BrianEnigma/chubby-tricorder/Images/probe.png

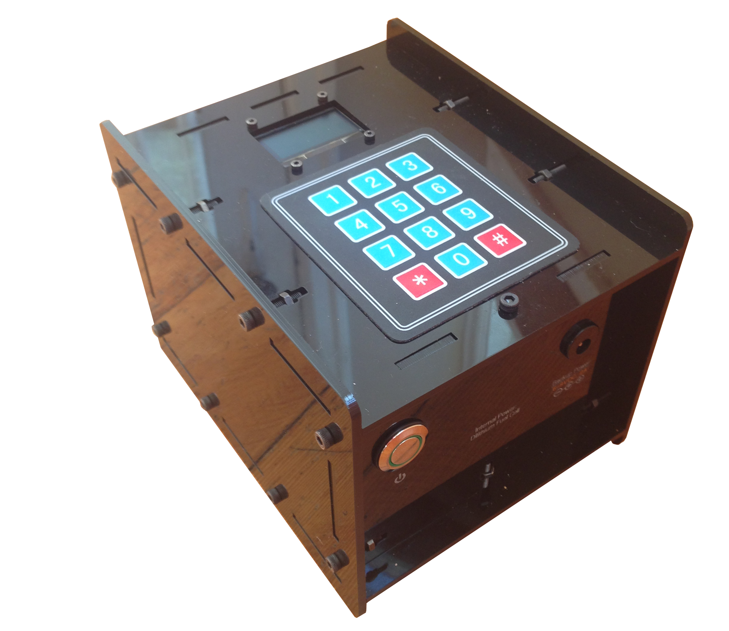
Images/probe.png
