BrianEnigma/chubby-tricorder/Images/Inspiration/romulan1.jpg

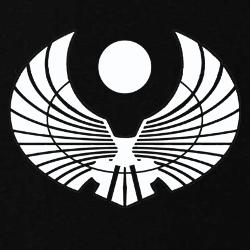
Images/Inspiration/romulan1.jpg
