BrianEnigma/chubby-tricorder/Images/Inspiration/romulan3.png

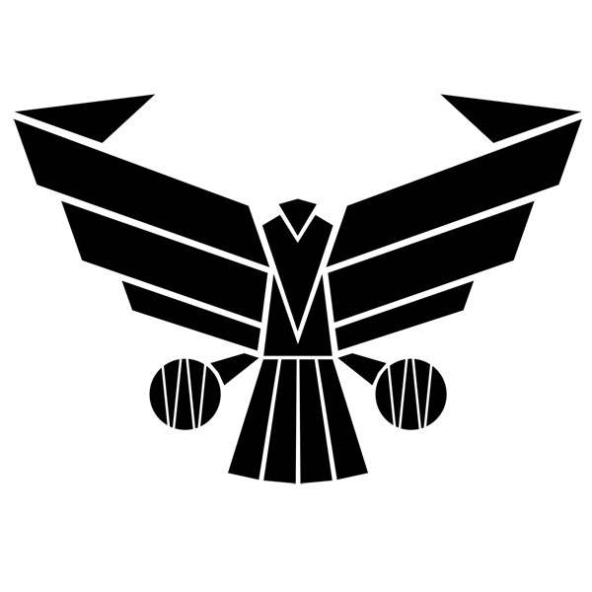
Images/Inspiration/romulan3.png
