BrianEnigma/chubby-tricorder/Images/Inspiration/romulan4.jpg

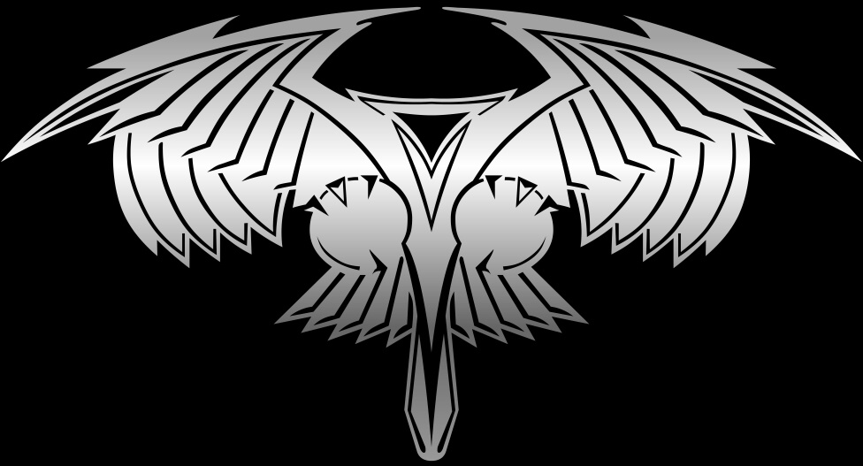
Images/Inspiration/romulan4.jpg
