BrianEnigma/chubby-tricorder/Images/Inspiration/Romulan_alphabet.gif

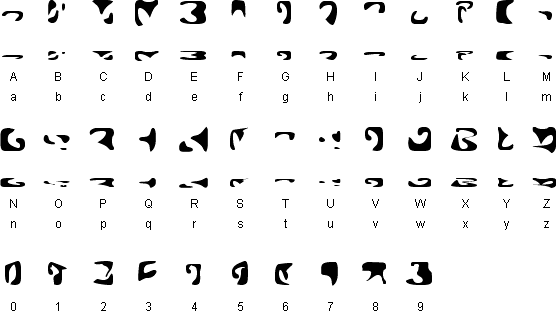
Images/Inspiration/Romulan_alphabet.gif
